Tinkerforge/stepper-brick/software/examples/mathematica/ExampleConfiguration.nb.txt

Needs["NETLink`"]
LoadNETAssembly["Tinkerforge",NotebookDirectory[]<>"../../.."]

host="localhost"
port=4223
uid="XXYYZZ"(*Change XXYYZZ to the UID of your Stepper Brick*)

(*Create IPConnection and device object*)
ipcon=NETNew["Tinkerforge.IPConnection"]
stepper=NETNew["Tinkerforge.BrickStepper",uid,ipcon]
ipcon@Connect[host,port]

stepper@SetMotorCurrent[800](*800 mA*)
stepper@SetStepMode[8](*1/8 step mode*)
stepper@SetMaxVelocity[2000](*Velocity 2000 steps/s*)

(*Slow acceleration (500 steps/s^2),*)
(*Fast deacceleration (5000 steps/s^2)*)
stepper@SetSpeedRamping[500,5000]

stepper@Enable[](*Enable motor power*)
stepper@SetSteps[60000](*Drive 60000 steps forward*)

Input["Click OK to exit"]

(*Stop motor before disabling motor power*)
stepper@Stop[](*Request motor stop*)
stepper@SetSpeedRamping[500,5000](*Fast deacceleration (5000 steps/s^2) for stopping*)
Pause[0.4](*Wait for motor to actually stop: max velocity (2000 steps/s) / decceleration (5000 steps/s^2) = 0.4 s*)
stepper@Disable[](*Disable motor power*)

ipcon@Disconnect[]
ReleaseNETObject[stepper]
ReleaseNETObject[ipcon]
